persianelectronic/LEOPARD_HD4/Image/Screenshot (166).png

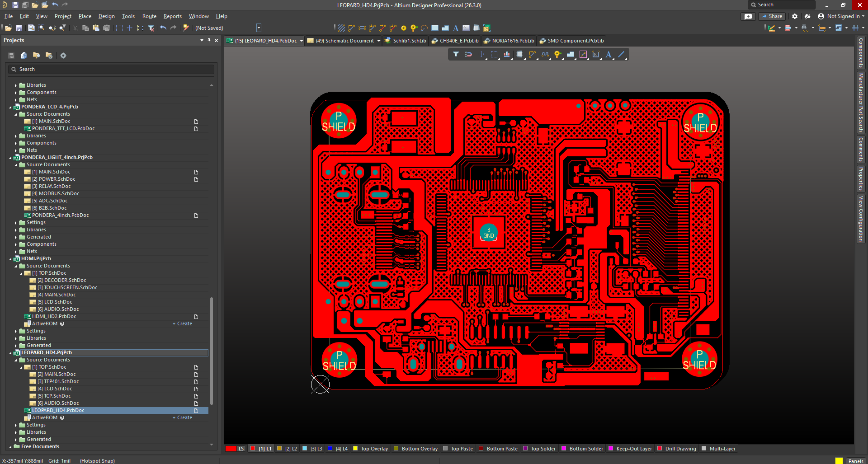
Image/Screenshot (166).png
