persianelectronic/LEOPARD_HD4/Image/IMG_20260217_180957.jpg

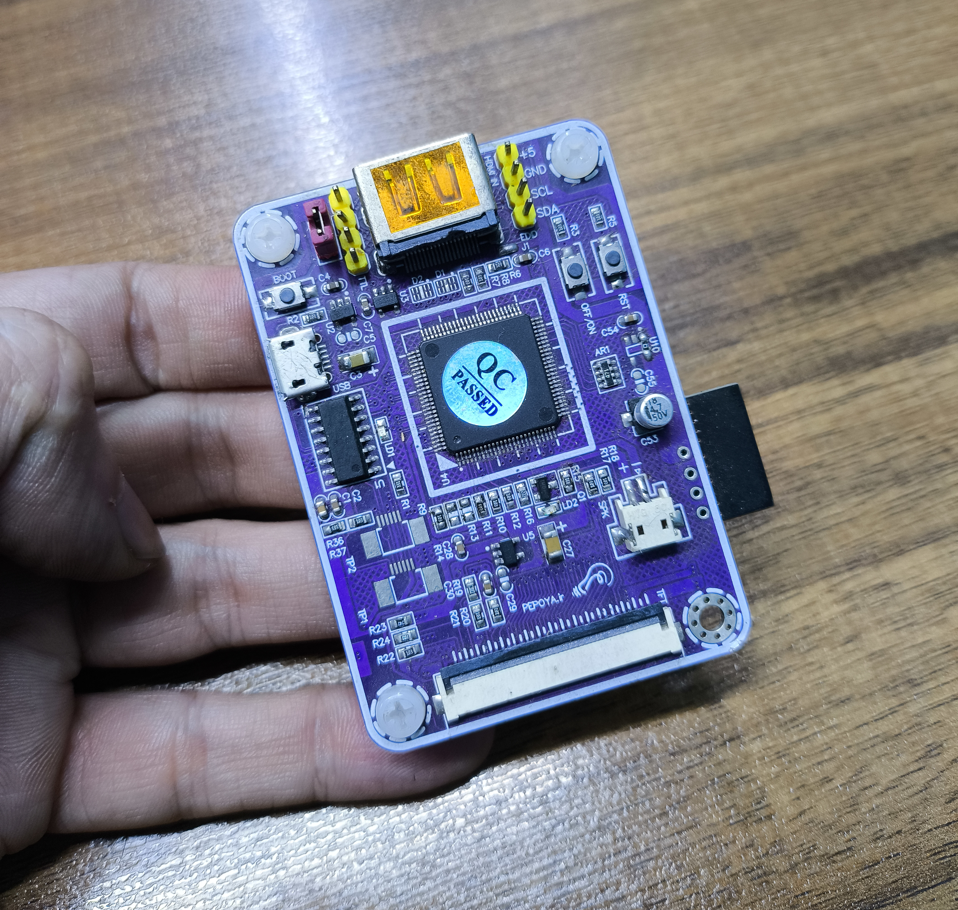
Image/IMG_20260217_180957.jpg
